palmerr23/ESP32-DCLOAD/Load_Touch_xTask_V3a/lscpiparser.cpp

/*
Copyright (c) 2013 Lachlan Gunn
Modified by RP 2020
- remove unneeded SI prefixes
-

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
THE SOFTWARE IS PROVIDED "AS IS", WITHOUT WARRANTY OF ANY KIND, EXPRESS OR
IMPLIED, INCLUDING BUT NOT LIMITED TO THE WARRANTIES OF MERCHANTABILITY,
FITNESS FOR A PARTICULAR PURPOSE AND NONINFRINGEMENT. IN NO EVENT SHALL THE
AUTHORS OR COPYRIGHT HOLDERS BE LIABLE FOR ANY CLAIM, DAMAGES OR OTHER
LIABILITY, WHETHER IN AN ACTION OF CONTRACT, TORT OR OTHERWISE, ARISING FROM,
OUT OF OR IN CONNECTION WITH THE SOFTWARE OR THE USE OR OTHER DEALINGS IN THE
SOFTWARE.
 */

#include <string.h>
#include <stdio.h>
#include <stdlib.h>
#include <ctype.h>

#include <Arduino.h>

#include "lscpiparser.h"

#ifdef __cplusplus

  extern "C" {
  
#endif
// moved scpi_error to mySCPI.h with registration of function
/*
static scpi_error_t
system_error(struct scpi_parser_context* ctx, struct scpi_token* command)
{
	struct scpi_error* error = scpi_pop_error(ctx);
	
	Serial.print(error->id);
        Serial.print(",\"");
        Serial.write((const uint8_t*)error->description, error->length);
	Serial.println("\"");

	scpi_free_tokens(command);
	return SCPI_SUCCESS;
}
*/
void
scpi_init(struct scpi_parser_context* ctx)
{
	struct scpi_command* system;
	struct scpi_command* error;
	
	ctx->command_tree = (struct scpi_command*)malloc(sizeof(struct scpi_command));
	
	ctx->command_tree->long_name = NULL;
	ctx->command_tree->long_name_length = 0;
	
	ctx->command_tree->short_name = NULL;
	ctx->command_tree->short_name_length = 0;
	
	ctx->command_tree->callback = NULL;
	ctx->command_tree->next = NULL;
	ctx->command_tree->children = NULL;

// moved registration of system and error to mySCPI - to allow further additions to them

	ctx->error_queue_head = NULL;
	ctx->error_queue_tail = NULL;
}

struct scpi_token*
scpi_parse_string( char* str, size_t length)
{
	int i;
	
	struct scpi_token* head;
	struct scpi_token* tail;
	
	int token_start;
	
	head = NULL;
	tail = NULL;
	token_start = 0;
	
	for(i = 0; i < length; i++)
	{
		
		if(str[i] == ':' || str[i] == ' ' || i == length-1)
		{
			struct scpi_token* new_tail;
			
			new_tail = (struct scpi_token*)malloc(sizeof(struct scpi_token));
			new_tail->type = 0;
			new_tail->value = str+token_start;
			new_tail->length = i-token_start;
			new_tail->next = NULL;
			
			if(i == length-1)
			{
				new_tail->length++;
			}
						
			if(tail == NULL)
			{
				head = new_tail;
			}
			else
			{
				tail->next = new_tail;
			}
			tail = new_tail;
			
			token_start = i+1;
			
			if(str[i] == ' ')
			{
				break;
			}
		}
	}
	
	token_start = -1;
	for(i++; i < length; i++)
	{
		if(token_start == -1 && !isspace(str[i]))
		{
			token_start = i;
		}
		
		if(str[i] == ',' || i == length-1)
		{
			struct scpi_token* new_tail;
			new_tail = (struct scpi_token*)malloc(sizeof(*new_tail));
			new_tail->type = 1;
			new_tail->value = str+token_start;
			new_tail->length = i-token_start;
			new_tail->next = NULL;
			
			if(i == length-1)
			{
				new_tail->length++;
			}
			
			tail->next = new_tail;
			tail = new_tail;
			
			token_start = -1;
		}
	}
	
	return head;
}

struct scpi_command*
scpi_register_command(struct scpi_command* parent, scpi_command_location_t location,
						const char* long_name,  size_t long_name_length,
						const char* short_name, size_t short_name_length,
						command_callback_t callback)
{
	
	struct scpi_command* current_command;
	
	if(location == SCPI_CL_CHILD)
	{
		current_command = parent->children;
	}
	else
	{
		current_command = parent;
	}
	
	if(current_command == NULL)
	{
		parent->children = (struct scpi_command*)malloc(sizeof(struct scpi_command));
		current_command = parent->children;
	}
	else
	{
		while(current_command->next != NULL)
		{
			current_command = current_command->next;
		}
		
		current_command->next = (struct scpi_command*)malloc(sizeof(struct scpi_command));
		current_command = current_command->next;
	}
	
	current_command->next = NULL;
	current_command->children = NULL;
	
	current_command->long_name = long_name;
	current_command->long_name_length = long_name_length;
	
	current_command->short_name = short_name;
	current_command->short_name_length = short_name_length;
	
	current_command->callback = callback;
	
	return current_command;
}

struct scpi_command*
scpi_find_command(struct scpi_parser_context* ctx,
					const struct scpi_token* parsed_string)
{
	struct scpi_command* root;
	const struct scpi_token* current_token;
	struct scpi_command* current_command;
	
	root = ctx->command_tree;
	current_token = parsed_string;
	current_command = root;

	
	while(current_token != NULL && current_token->type == 0)
	{
	
		int found_token = 0;
		while(current_command != NULL)
		{
			
			if((current_token->length == current_command->long_name_length
					&& !memcmp(current_token->value, current_command->long_name, current_token->length))
				|| (current_token->length == current_command->short_name_length
					&& !memcmp(current_token->value, current_command->short_name, current_token->length)))
			{
				/* We have found the token. */
				current_token = current_token->next;
				
				if(current_token == NULL || current_token->type != 0)
				{
					return current_command;
				}
				else
				{
					found_token = 1;
					current_command = current_command->children;
					break;
				}
			}
			else
			{
				current_command = current_command->next;
			}
		}
		
		if(!found_token)
		{
			return NULL;
		}
	}
	
	return NULL;
}

scpi_error_t
scpi_execute_command(struct scpi_parser_context* ctx,  char* command_string, size_t length)
{
	struct scpi_command* command;
	struct scpi_token* parsed_command;
	
	parsed_command = scpi_parse_string(command_string, length);
	//Serial.printf("SCPI CMD [%s], len = %i\n", command_string, length);
	//Serial.printf("SCPI parsed [%s]\n", parsed_command->value );
	
	command = scpi_find_command(ctx, parsed_command);
	if(command == NULL)
	{
		return SCPI_COMMAND_NOT_FOUND;
	}
	
	if(command->callback == NULL)
	{
		return SCPI_NO_CALLBACK;
	}
	
	
	return command->callback(ctx, parsed_command);
}

void
scpi_free_some_tokens(struct scpi_token* start, struct scpi_token* end)
{
	struct scpi_token* prev;
	while(start != NULL && start != end)
	{
		prev = start;
		start = start->next;
		
		free((void*)prev);
	}
}

void
scpi_free_tokens(struct scpi_token* start)
{
	scpi_free_some_tokens(start, NULL);
}

// parses integers and floats in decimal formats
// also parses units
// prefixes are absorbed and the appropriate multiplier applied to the (float).value returned
// a unit (V, A, etc) is returned as output_numeric.unit[0]
// the parser is overly tolerant of incorrect "unit" characters
struct scpi_numeric
scpi_parse_numeric(const char* str, size_t length, float default_value, float min_value, float max_value)
{
	int i;
	float mantissa;
	int state;
	int sign;
	int point_position;
	int exponent;
	int exponent_sign;
	float exponent_multiplier;
	float value;
	const char* unit_start;
	const char* unit_end;
	struct scpi_numeric retval;
	
	exponent = 0;
	exponent_sign = 0;
	point_position = 0;
	sign = 0;
	state = 0;
	mantissa = 0;
	exponent_multiplier = 1;
	unit_start = NULL;
	unit_end = NULL;
	//if(length > 7) length = 7;

	for(i = 0; i < length; i++)
	{
		if(state == 0)
		{
			/* Remove leading whitespace */			
			if(isspace(str[i]))
			{
				continue;
			}				// added short form of DEFAULT
                        else if((length-i >= 7 && str[i]   == 'D' && str[i+1] == 'E' && str[i+2] == 'F'
                                               && str[i+3] == 'A' && str[i+4] == 'U' && str[i+5] == 'L'
                                               && str[i+6] == 'T') 
							 || (length-i >= 4 && str[i]   == 'D' && str[i+1] == 'E' && str[i+2] == 'F'
                                               && str[i+3] == 'A' )
								)
                        {
                                /* The user has asked for the default value. */
                                retval.value = default_value;
                                retval.unit = NULL;
                                retval.length = 0;
                                
                                return retval;
                        }
                        else if(length-i >= 3 && str[i] == 'M' && str[i+1] == 'A' && str[i+2] == 'X')
                        {
                                /* The user has asked for the maximum value. */
                                retval.value = max_value;
                                retval.unit = NULL;
                                retval.length = 0;
                                return retval;
                        }
                        else if(length-i >= 3 && str[i] == 'M' && str[i+1] == 'I' && str[i+2] == 'N')
                        {
                                /* The user has asked for the minimum value. */
                                retval.value = min_value;
                                retval.unit = NULL;
                                retval.length = 0;
                                return retval;
                        }
			else if(str[i] == '+' || str[i] == '-')
			{
				/* We have hit a +/- */
				state = 1;
			}
			else if(isdigit(str[i]))
			{
				/* We have reached the number itself. */
				state = 2;
			}
			else
			{
				state = -1;
				continue;
			}
		}
		
		if(state == 1)
		{
			/* Set the sign. */
			if(str[i] == '+')
			{
				sign = 0;
			}
			else
			{
				sign = 1;
			}
			
			state = 2;
			continue;
		}
		
		if(state == 2 || state == 3)
		{
			if(isdigit(str[i]))
			{
				/* Start accumulating digits. */
				mantissa = (10*mantissa) + (float)(str[i] - 0x30);
				//Serial.printf("[%c, %i]%5.1f ",str[i], str[i] - 0x30, mantissa);
				if(state == 3)
				{
					/* We are past the decimal point, so reposition it. */
					point_position++;
				}
			}
			else if(str[i] == '.')
			{
				state = 3;
				continue;
			}
			else if(str[i] == 'e')
			{
				state = 4;
				continue;
			}
			else
			{
				state = 6;
			}
		}
		
		if(state == 4)
		{
			/* We are now looking at the exponent sign. */
			if(str[i] == '+' || str[i] == '-')
			{
				if(str[i] == '-')
				{
					exponent_sign = 1;
				}
			}
			else if(isdigit(str[i]))
			{
				state = 5;
			}
			else
			{
				state = -1;
			}
		}
		
		if(state == 5)
		{
			
			if(isdigit(str[i]))
			{
				exponent = (exponent*10) + (int)(str[i] - 0x30);
				continue;
			}
			else
			{
				state = 6;
			}
		}
		
		if(state == 6)
		{
		
			/* Remove spaces between the number and its units. */
			if(isspace(str[i]))
			{
				continue;
			}
			else
			{
				state = 7;
			}
		
		}
		
		if(state == 7)
		{
			/* The unit itself---first the multiplier. */
			/* RP removed all uncommon multipliers cCdDm and all > 1000 */
			switch(str[i])
			{
				
				case 'm':
					exponent -= 3;
					state = 8;
                                        continue;
                                        break;
				
				
				case 'k':
					exponent += 3;
					state = 8;
                                        continue;
                                        break;
				
				
				default:
				
					if(isupper(str[i]))
					{
						state = 8;
					}
					else
					{
						state = -1;
                                                continue;
					}
			}

		}
		
		if(state == 8)
		{
			/* The unit proper. */
			if(isalpha(str[i]))
			{
				if(unit_start == NULL)
				{
					unit_start = str+i;
				}
				state = 9;
			}
			else
			{
                                if(unit_start != NULL)
                                {
				        unit_end = str+i;
                                }
                                else
                                {
                                        unit_end = NULL;
                                }
			
				state = -1;
			}
		}
	}

        if(unit_start != NULL && unit_end == NULL)
        {
          unit_end = str+length-1;
        }
	
	value = (float)mantissa;
	
	if(exponent_sign != 0)
	{
		exponent = -exponent;
	}
	
	exponent -= point_position;
	if(exponent > 0)
	{
		for(i = 0; i < exponent; i++)
		{
			exponent_multiplier *= 10;
		}
		
		value *= exponent_multiplier;
	}
	else
	{
		for(i = exponent; i < 0; i++)
		{
			exponent_multiplier *= 10;
		}
		
		value /= exponent_multiplier;
	}
	//Serial.printf("M: %5.1f, E: %i, EM: %5.1g\n", mantissa, exponent, exponent_multiplier);
	
	if(sign != 0)
	{
		value = -value;
	}
	
	retval.value  = value;
	retval.unit   = unit_start;
	
	if(unit_start == NULL)
	{
		retval.length = 0;
	}
	else
	{
		retval.length = unit_end - unit_start + 1;
	}
	
	
	return retval;
}

void
scpi_queue_error(struct scpi_parser_context* ctx, struct scpi_error error)
{
	struct scpi_error* new_error;
	
	new_error = (struct scpi_error*)malloc(sizeof(struct scpi_error));
	new_error->id = error.id;
	new_error->description = error.description;
	new_error->length = strlen(new_error->description);// error.length;
	
	new_error->next = NULL;
	
	if(ctx->error_queue_head != NULL)
	{
		ctx->error_queue_tail->next = new_error;
	}
	else
	{
		ctx->error_queue_head = new_error;
	}
	
	ctx->error_queue_tail = new_error;
}

struct scpi_error*
scpi_pop_error(struct scpi_parser_context* ctx)
{
	if(ctx->error_queue_head == NULL)
	{
		struct scpi_error* success;
		
		success = (struct scpi_error*)malloc(sizeof(struct scpi_error));
		success->id = 0;
		success->description = (char *)"No error";
		success->length = 8;
		
		return success;
	}
	else
	{
		struct scpi_error* retval;

		retval = ctx->error_queue_head;
		ctx->error_queue_head = retval->next;
		
		if(ctx->error_queue_head == NULL)
{
			ctx->error_queue_tail = NULL;
		}
		
		return retval;
	}
}

#ifdef __cplusplus

  }
  
#endif
