palmerr23/ESP32-DCLOAD/Load_Touch_xTask_V3a/myLADS1115bits.h

/* 
 * ADS1115bits - ISR that can't go into the library
 */
 #ifndef __LADSB1115_H__
#define __LADSB1115_H__
#include "myLADS1115.h"
float ADStoV(int ADCval);
float ADStoA(int ADCval);

// outside the object definition (ISR & child routines can't be in object)
volatile long adsISRcount = 0;
volatile bool adsReady = false, adsSetready = false;
long adSProcessCount = 0;
uint8_t adsMux = ADSMUX_START;
#define NUMADC 2   // ADS differeential mode
#define NUMESPADC 3 // single ended 
//int16_t espReadings[NUMESPADC];
uint8_t espPins [NUMESPADC] = {ADC_BV, ADC_BI, ADC_BT};
int16_t adsReadings[NUMADC];
// Voltage filter to eliminate transients
#define NUM_AVG_VOLTS 8 // average over N readings
#define AVG_USE 10       // only use every Nth reading to avoid short runs of erratic voltage readings
bool _avg_ready = false; // first run at average after ON is complete
float batVolts[NUM_AVG_VOLTS];

const uint16_t adsConfig =
      ADS1015_REG_CONFIG_CQUE_1CONV | // Assert ALERT/RDY after one conversions
      ADS1015_REG_CONFIG_CPOL_ACTVLOW |       // Alert/Rdy active low   (default val)
      ADS_RATE |                              // sample rate selected above
      ADS1015_REG_CONFIG_MODE_SINGLE;         // Single-shot mode (default)
      //ADS1015_REG_CONFIG_CLAT_LATCH |  //  Latching comparator
      //ADS1015_REG_CONFIG_CMODE_STAD |   // Traditional comparator (default val)
      //ADS1015_REG_CONFIG_OS_SINGLE ;   // single shot start      
      // ADS1115_REG_CONFIG_MUX_SE |      // single ended conversion
      // ADS1015_REG_CONFIG_PGA_4_096V;   // PGA GAIN = 1 

//long adsWdt; // ADS watchdog
void adsProcess(void){
  if (adsReady) 
  {	
    // convert latest reading to "counts read" and "read-world" values
		// conversions now done just before control() 
    // reading conversion register resets DRDY interrupt pulse.
	  switch (adsMux)
	  {
		case (ADSMUXV): // 0
	      ADCcount.ADSv = ads.getLastConversionResults();
	      meas.ADSvolts = ADStoV(ADCcount.ADSv);
		  if (!_outOn) // no load voltage used in estimating DUT ESR in CV mode
		  {
			_lastVolts = meas.ADSvolts;
			_lastAmps = 0.0;
		  }
	      break;
	    case (ADSMUXI):  // 1
	      ADCcount.ADSa = ads.getLastConversionResults();
	      meas.ADSamps = ADStoA(ADCcount.ADSa);
		  break;
	  }
     
    if(adsMux == 1) // flag a complete set of readings, immediately after a current reading.
    {
      adSProcessCount++;  // updated each 2 cycles = 2.3mS @ 860 sps
      adsSetready = true; // complete set of readings has been processed
    }   
						   
    // start next reading
	  adsMux = ++adsMux % NUMADC;
	  // don't bother about turning interrupts off - single shot mode
//    ads.adsStartSingleDiffRdy(adsConfig | ADS_GAIN, adsMux); 
    adsReady = false; // already processed
  	//adsWdt = millis();
  	//Serial.print("^");
  }
}

// ADS voltage filter
// circular list
// discard hi/low values 
// use every Nth reading
int avp = 0;
int avg_cnt = 0;

// called from ADS processing after a new reading cycle has completed
void averageVolts(void)
{
  if(avg_cnt++ != AVG_USE)  
    return; 
  else
    avg_cnt = 0;
    
  float hi = -999.0;
  float lo = 999.0;
  float tot = 0.0;
  batVolts[avp] = meas.ADSvolts;  // add new reading
  if(++avp == NUM_AVG_VOLTS)
  {
    _avg_ready = true;
    avp = 0;
  }
  //avp = ++avp % NUM_AVG_VOLTS;
  for(int i = 0; i < NUM_AVG_VOLTS; i++) 
  {   
      tot += batVolts[i];
      // find max and min values
      if(batVolts[i] > hi) 
        hi = batVolts[i];
      if(batVolts[i] < lo)
        lo = batVolts[i];      
  }    
  meas.ADSvoltsAvg = (tot - hi - lo) / float(NUM_AVG_VOLTS -2); // average less hi & lo 
}
void adsReadStart(bool reStart = false)
{
    if(reStart) 
    {
      ads.getLastConversionResults(); //reset conversion complete (RDY) pin
      //Serial.printf("ADS restarting\n");
    }
   ads.adsStartSingleDiffRdy(adsConfig | ADS_GAIN, adsMux); // any channel will do, sorted out next cycle
   // adsLastInt = millis(); // stop double triggering of the reset
   adsReady = false; 
   adsISRcount = 0;
  
}

void adsTest()
{
 // start ADS1115 ADC
 int rdg;
  ads.setGain(ADS_GAIN);        // 1x gain   +/- 4.096V  1 bit = 2mV      0.125mV
  pinMode(ADSRDY, INPUT_PULLUP);
  ads.begin(400000);  // I2C speed, 1000000 (1M = FMPlus) is probably OK, 400000 is safe
  Serial.println("ADS BEGIN done");
  Wire.beginTransmission (ADS_ADDR);
	if (Wire.endTransmission () == 0)
		Serial.printf("Found ADS1115 at 0x%x\n", ADS_ADDR);
	else
		Serial.printf("ADS1115 not found at 0x%x\n", ADS_ADDR);
  //  delay(100);
  //attachInterrupt(digitalPinToInterrupt(ADSRDY), ads_ISR, FALLING);
 // Serial.println("ATTACH int done");
 delay(1000);
  while(1)
  {
	  for (int i = 0; i < 4; i++)
	  {
		//rdg = ads.readADC_SingleEnded(i);		
		ads.adsStartSingleRdy(adsConfig,i); // no wait, needs suitable delay before reading
		delay(2);
		rdg = ads.getLastConversionResults();	
		Serial.printf("ADS ch[%i] = %i\n", i, rdg);
	  }
	  Serial.println();
	  delay(40);
  }
}
void printADSconfig(void)
{
	uint16_t rreg = ads.readReg(ADS_ADDR,1);
	Serial.printf("\nADS config: MUX 0x%01x, PGA 0x%01x, Mode 0x%01x, SPS 0x%1x, Modes 0x%02x\n", (rreg >> 12) & 0x7, (rreg >> 9) & 0x7, (rreg >> 8) & 0x1, (rreg >> 5) & 0x7, (rreg) & 0x1f);
	  
}
#endif
