palmerr23/ESP32-DCLOAD/Load_Touch_xTask_V3a/myLESP32ADC_xxx.h

/* IS_ESP32 ADC
NO LONGER USED
*/
#ifndef LESP32ADC_H
#define LESP32ADC_H
//#define EEPROM_SIZE 4096 // bytes available

// return read value in Volts - identically named for different inbuilt ADCs
 //three point linearisation - corrects increase in slope from 3000 counts onward
//hal_cal ESPADC_HAL = {0, 0.129, 2.731, 3.163, 3296, 0, 12, true}; // ESP ADC
//#include "myLcvtHAL.h"
/*
#define ADCREADS 4
float  readADCHAL(uint8_t ADCpin){
	// ADCchannel is a IS_ESP32 pin reference
	// devAddr is ignored  
	int reading = 0;
	float volts;
	for (short i = 0; i < ADCREADS; i++)
		reading += analogRead(ADCpin);
	reading /= ADCREADS;
	volts = convertHAL(reading, &ESPADC_HAL);
	return volts;
}
float  readVolts(uint8_t ADCpin)
{
	float volts = convertHAL(readADCHAL(ADCpin), &ESPADC_HAL);
	return volts;
}
*/
#endif
